tradwiki/Read_Signals/DrawPlanck-2.0/Draw_Planck_2_0/bg_3.png

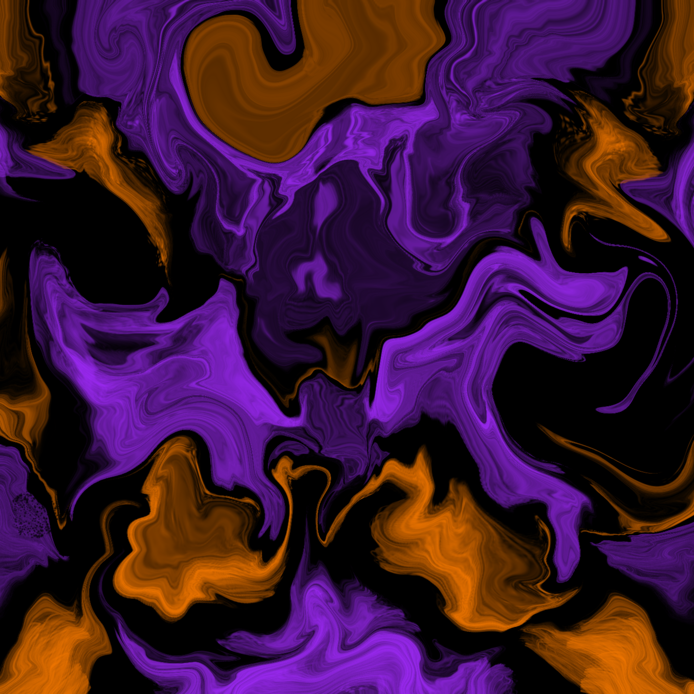
DrawPlanck-2.0/Draw_Planck_2_0/bg_3.png
