tradwiki/Read_Signals/DrawPlanck-2.0/Draw_Planck_2_0/carbone_riverain.png

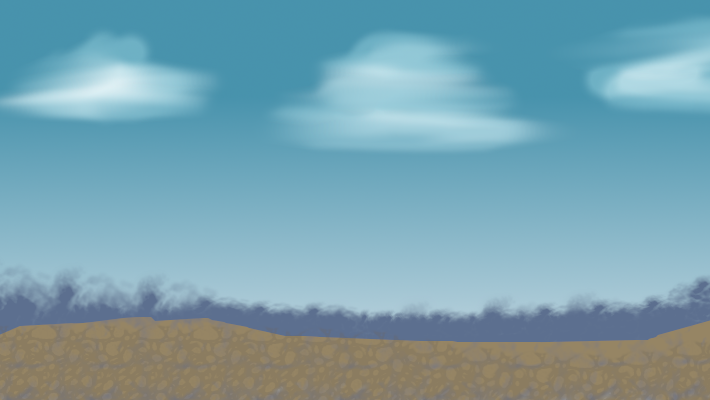
DrawPlanck-2.0/Draw_Planck_2_0/carbone_riverain.png
