tradwiki/Read_Signals/DrawPlanck-2.0/Draw_Planck_2_0/menu_bg.png

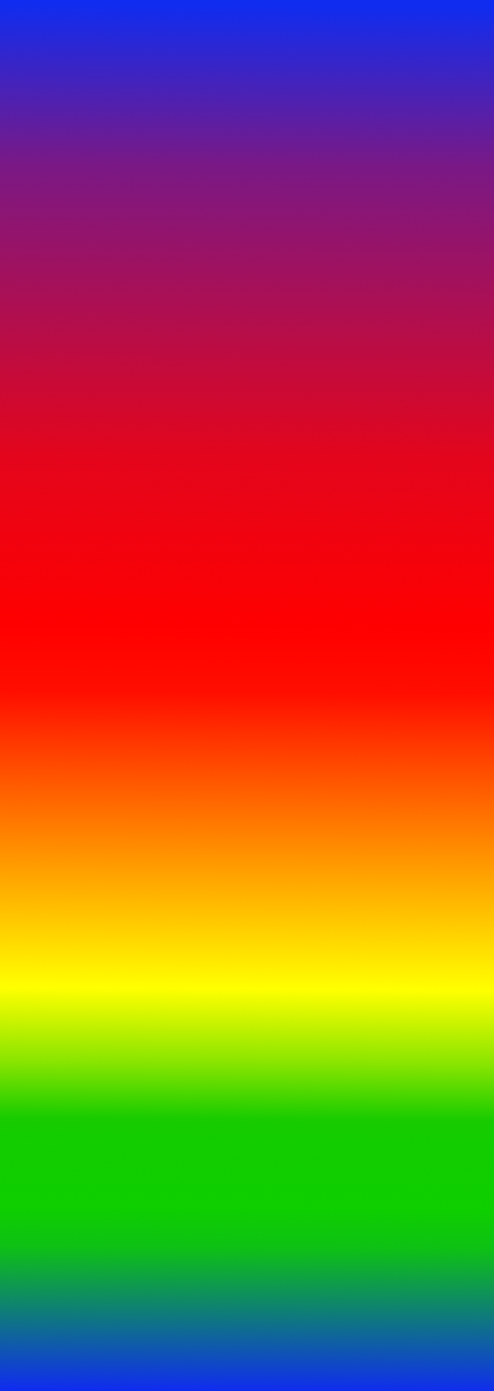
DrawPlanck-2.0/Draw_Planck_2_0/menu_bg.png
