tradwiki/Read_Signals/DrawPlanck-2.0/Draw_Planck_2_0/ScrollRect.pde

class ScrollRect {

  float rectPosX=0;
  float rectPosY=0;
  float rectWidth=14; 
  float rectHeight=30;

  boolean holdScrollRect=false; 

  float offsetMouseY; 

  //constr
  ScrollRect() {
    // you have to make a scrollRect in setup after size()
    rectPosX=width-rectWidth-1;
  }//constr

  void display() {
    fill(122);
    stroke(0);
    line (rectPosX-1, 0, 
      rectPosX-1, height);
    rect(rectPosX, rectPosY, 
      rectWidth, rectHeight);

    // Three small lines in the center   
    centerLine(-3); 
    centerLine(0);
    centerLine(3);
  }

  void centerLine(float offset) {
    line(rectPosX+3, rectPosY+rectHeight/2+offset, 
      rectPosX+rectWidth-3, rectPosY+rectHeight/2+offset);
  }

  void mousePressedRect() {
    if (mouseOver()) {
      holdScrollRect=true;
      offsetMouseY=mouseY-rectPosY;
    }
  }

  void mouseReleasedRect() {
    scrollRect.holdScrollRect=false;
  }

  void update() {
    // dragging of the mouse 
    if (holdScrollRect) {
      rectPosY=mouseY-offsetMouseY;
      if (rectPosY<0)
        rectPosY=0;
      if (rectPosY+rectHeight>height-1)
        rectPosY=height-rectHeight-1;
    }
  }

  float scrollValue() {
    return 
      map(rectPosY, 
      0, height-rectHeight, 
      0, - (heightOfCanvas - height));
  }

  boolean mouseOver() {
    return mouseX>rectPosX&&
      mouseX<rectPosX+rectWidth&&
      mouseY>rectPosY&&
      mouseY<rectPosY+rectHeight;
  }//function 
  //
}
